IntelliFire-UofG/IntelliFireCore/src/IntelliFireUI/include/keyLogger.h

#ifndef KEYLOGGER_H
#define KEYLOGGER_H

#include <QWidget>
#include <QKeyEvent>
#include <functional>
enum class KeyEventType {
    NULL_EVENT,
    KEY_PRESSED,
    KEY_RELEASED
};
struct KeyEventInfo {
    KeyEventType eventType = KeyEventType::NULL_EVENT;
    QString keyName;
    int keyCode;
    QString rawText;

    KeyEventInfo(KeyEventType event_type, QString name, int code, QString text)
        : eventType(event_type), keyName(name), keyCode(code), rawText(text) {}
};

class KeyLogger : public QWidget {
    Q_OBJECT

public:
    explicit KeyLogger(QWidget *parent = nullptr);

    /**
     * @brief Set a callback function to handle key events.
     * @param callback The function to be executed when a key event occurs.
     */
    void setKeyCallback(std::function<void(KeyEventInfo)> callback);

    /**
     * @brief Handles key press events.
     * @param event The key event data.
     */
    void keyPressEvent(QKeyEvent *event) override;

    /**
     * @brief Handles key release events.
     * @param event The key event data.
     */
    void keyReleaseEvent(QKeyEvent *event) override;
   
private:
    std::function<void(const KeyEventInfo&)> keyCallback;
};

#endif // KEYLOGGER_H
