IntelliFire-UofG/IntelliFireCore/src/IntelliFireUI/src/ads1115manager.cpp

// ads1115manager.cpp
#include "ads1115manager.h"
#include <stdexcept>
#include <cstdio>
#include <mutex>

ADS1115Manager::ADS1115Manager(QObject *parent) : QObject(parent) {
    ads1115rpi.registerCallback(this);
}

ADS1115Manager::~ADS1115Manager() {
    stop();
}

void ADS1115Manager::start() {
    ADS1115settings s;
    s.samplingRate = ADS1115settings::FS128HZ;
    s.pgaGain = ADS1115settings::FSR4_096;
    s.drdy_chip = 4; // For RPI1-4: chip = 0. For RPI5: chip = 4.

    try {
        ads1115rpi.start(s);
    }catch (std::runtime_error &e) {
        printf("I2C error: %s \n", e.what());
    }
}

void ADS1115Manager::stop() {
    ads1115rpi.stop();
}

void ADS1115Manager::hasADS1115Sample(float v) {
    std::lock_guard<std::mutex> lock(sample_mutex);

    if (discard) {
        discard = false;
        return;
    }

    sensorValues[current_channel] = v;
    emit newSensorValue(current_channel, v);

    nextChannel();
    discard = true; // Cycle through 4 sensors
}

void ADS1115Manager::nextChannel() {
    switch (current_channel) {
        case ADS1115settings::AIN0:
            current_channel = ADS1115settings::AIN1;
            break;
        case ADS1115settings::AIN1:
            current_channel = ADS1115settings::AIN2;
            break;
        case ADS1115settings::AIN2:
            current_channel = ADS1115settings::AIN3;
            break;
        case ADS1115settings::AIN3:
            current_channel = ADS1115settings::AIN0;
            break;
    }

    ads1115rpi.setChannel(current_channel);
}
